ISEN-Lille-CRYSTEO/Coupe-de-France-2018/plateauV2/plateauV2.ino

#include "plateauV2.h"

//=== CONSTANTES ===
#define encodeuseGaucheAvant 13 //encodeur gauche A
#define encodeuseDroiteAvant 11 //encodeur droit A
#define encodeuseGaucheArriere 12 //encodeur gauche A
#define encodeuseDroiteArriere 10 //encodeur droit A
#define pinTrigger 31 // pin du capteur Trigger
// === Variable ===
CDF_plateau plateau(pinTrigger);

void setup() {
	Serial.begin(115200);
 	plateau.asservisement = CDF_asservisement(13,12,11,10,6,3,22,23,52,53);// regarde le README.md
	attachInterrupt(digitalPinToInterrupt(encodeuseGaucheAvant), [&](){plateau.asservisement.compteur_tick_L();}, RISING);
 	attachInterrupt(digitalPinToInterrupt(encodeuseDroiteAvant), [&](){plateau.asservisement.compteur_tick_R();}, RISING);
	// le roboot se rend au point..
	plateau.ajout(std::pair<Point,bool> (Point{0.3,0},true));
	plateau.ajout(std::pair<Point,bool> (Point{-0.15,0},true));
	// le roboot lance sont programme principale
	plateau.Lancement();
}

void loop() {
}
