ISEN-Lille-CRYSTEO/Coupe-de-France-2018/asservisement/asservisementv4/asservisementv4.cpp

#include "asservisementv4.h"

CDF_asservisement::CDF_asservisement(){
	//constructeur par défaut
}

CDF_asservisement::CDF_asservisement(int pinEGAvant,int pinEGArriere,int pinEDAvant,int pinEDArriere,int PDroit,int PGauche,int MAvantMG,int MArrierMG,int MAvantMD,int MArrierMD){
  this->pinEGAvant = pinEGAvant;
  this->pinEGArriere = pinEGArriere;
  this->pinEDAvant = pinEDAvant;
  this->pinEDArriere = pinEDArriere;
  this->PDroit = PDroit;
  this->PGauche = PGauche;
  this->MAvantMG = MAvantMG;
  this->MArriereMG = MArrierMG;
  this->MAvantMD = MAvantMD;
  this->MArriereMD = MArrierMD;
  //=== Encodeuse ===
  pinMode(this->pinEGAvant,INPUT);
  pinMode(this->pinEGArriere,INPUT);
  pinMode(this->pinEDAvant,INPUT);
  pinMode(this->pinEDArriere,INPUT);
  //=== Motor ===
  pinMode(this->PDroit,OUTPUT);
  pinMode(this->PGauche,OUTPUT);
  pinMode(this->MAvantMG,OUTPUT);
  pinMode(this->MArriereMG,OUTPUT);
  pinMode(this->MAvantMD,OUTPUT);
  pinMode(this->MArriereMD,OUTPUT);
  //=== Allumage des motor ===
  digitalWrite(this->MAvantMG,LOW);
  digitalWrite(this->MArriereMG,LOW);
  digitalWrite(this->MAvantMD,LOW);
  digitalWrite(this->MArriereMD,LOW);
}

void CDF_asservisement::compteur_tick_R1(){
  if(this->sens)
  	this->tick_codeuse_R++;
  else
    this->tick_codeuse_R--;
}
void CDF_asservisement::compteur_tick_R2(){
  if(this->sens)
  	this->tick_codeuse_R++;
  else
    this->tick_codeuse_R--;
}
void CDF_asservisement::compteur_tick_L1(){
  if(this->sens)
 	  this->tick_codeuse_L++;
  else
    this->tick_codeuse_L--;
}
void CDF_asservisement::compteur_tick_L2(){
  if(this->sens)
 	  this->tick_codeuse_L++;
  else
    this->tick_codeuse_L--;
}

double CDF_asservisement::avancement(int sens){
  this->sens = sens;
	digitalWrite(this->MAvantMD,sens);
	digitalWrite(this->MAvantMG,sens);
  digitalWrite(this->MArriereMD,!sens);
  digitalWrite(this->MArriereMG,!sens);
  delay(10);
  analogWrite(this->PDroit,this->valR);
 	analogWrite(this->PGauche,this->valL);
  this->diff = calculDistance(this->tick_codeuse_R/2) -  calculDistance(this->tick_codeuse_L/2);
  this->controle();
  if(this->diff >= 0)
    return calculDistance(this->tick_codeuse_R/2);
  else
    return calculDistance(this->tick_codeuse_L/2);
}

double CDF_asservisement::rotation(double degree){
  this->arret();
  if(degree >= 0)
    this->valeur = true;
  else
    this->valeur = false;

	digitalWrite(this->MAvantMG,!valeur);
 	digitalWrite(this->MAvantMD,valeur);
 	delay(10); // on inverse un des 2 motor.
 	digitalWrite(this->MArriereMG,valeur);
 	digitalWrite(this->MArriereMD,!valeur);

  this->valL = 220;
  this->valR = 220;
 	analogWrite(this->PDroit,this->valR);
 	analogWrite(this->PGauche,this->valL);
 	while(calculDistance(this->tick_codeuse_R/2) < Tour*abs(degree/360) && calculDistance(this->tick_codeuse_L/2) < Tour*abs(degree/360)){
    this->diff = pow(-1,valeur+1)*(calculDistance(this->tick_codeuse_R/2) +  calculDistance(this->tick_codeuse_L/2));
    this->controle();
  }
  this->arret();
  this->valL = MinP;
  this->valR = MinP;
}

double CDF_asservisement::calculDistance(double tick_codeuse){
 	double nombre_tours = abs((double) tick_codeuse) / (double) nombreTicksPour1TourDeRoue;
 	double metre_parcourue = (double) nombre_tours * (double) perimetreRoueCodeuse; // en mêtres
 	return (double) metre_parcourue;
}

void CDF_asservisement::controle(){
  if(this->diff <-(1/100)*((double)MinP/2*(double)MaxP)*exp((double)MinP/2*(double)MaxP)){
     this->valL += 1;
     if(this->valL > MaxP)
       this->valL = MaxP;
  }
  else if(this->diff > (1/100)*((double)MinP/2*(double)MaxP)*exp((double)MinP/2*(double)MaxP)){
     this->valR += 1;
     if(this->valR > MaxP)
        this->valR = MaxP;
  }
  else {//Si non vitesse constance
    if(this->valL > MinP)
      this->valL -= 1;
    if(this->valR > MinP)
      this->valR -= 1;
  }
  delay(1);
}

void CDF_asservisement::arret(){
  while(this->valL < 254 || this->valR < 254){
    analogWrite(this->PDroit,this->valL++);
    analogWrite(this->PGauche,this->valR++);
    delay(1);
  }
  analogWrite(this->PDroit,MaxP);
  analogWrite(this->PGauche,MaxP);
  digitalWrite(this->MArriereMG,LOW);
 	digitalWrite(this->MArriereMD,LOW);
  digitalWrite(this->MAvantMG,LOW);
 	digitalWrite(this->MAvantMG,LOW);
  delay(1000);
  this->tick_codeuse_R = 0;
  this->tick_codeuse_L = 0;
}
